AlexanderHD27/oscilloscope-rendering/circuits/dac-pcb/dac-pcb.png

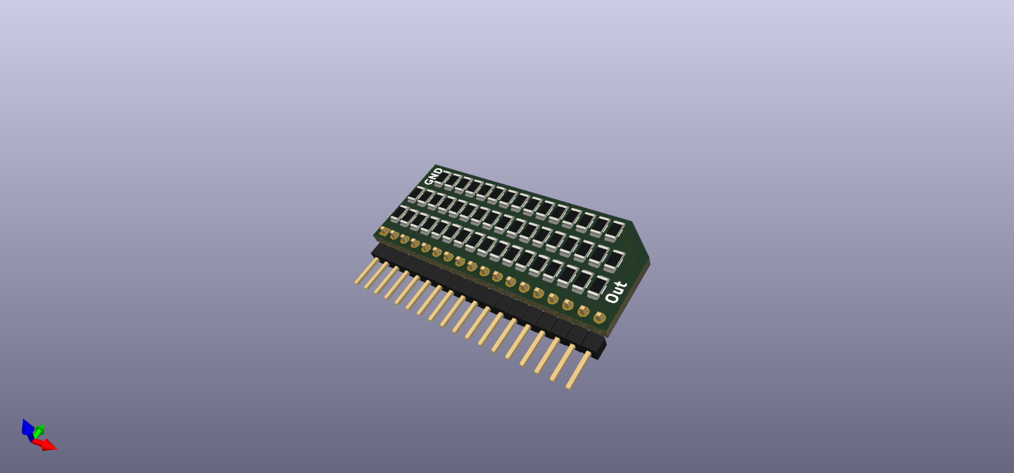
circuits/dac-pcb/dac-pcb.png
