AlexanderHD27/oscilloscope-rendering/tools/Op-Amp_Inverting_Amplifier.svg.png

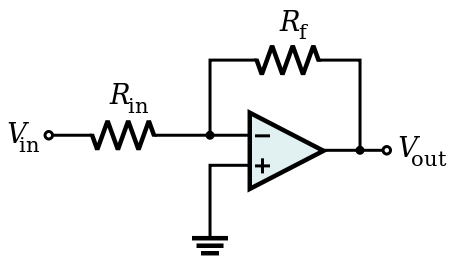
tools/Op-Amp_Inverting_Amplifier.svg.png
