AlexanderHD27/oscilloscope-rendering/circuits/rpi-pico-wiring/rpi-pico-wiring.kicad_pcb

## KiCad design NABU/NABU-01.kicad_sch


Parts:
C1, C2: 680pF
J17: 4K/8K_JUMPER
PH1: NABU-01
R1: 680Ω
R2, R3, R4: 3.3K
R5, R6, R7: 33Ω
U9, U37, U57: LS32
U28: LS38
U38: LP76-57
U39: LS00
U42: HM4864-2_(U42..U49)
U50: 33Ω
U51: LS157_(U51)
U52: LS157_(U52)
U53: 2732/2764
U54: Z80
U55: LS260
U56: LS04
U58: LS74

Connections:
3.58: U58.
+5V: R1.1, R2.1, R3.1, R4.1, U53., U54., U58.
A0: U52., U53., U54.
A1: U52., U53., U54.
A2: U52., U53., U54.
A3: U52., U53., U54.
A4: U51., U53., U54.
A5: U51., U53., U54.
A6: U51., U53., U54.
A7: U51., U53., U54.
A8: U52., U53., U54.
A9: U52., U53., U54.
A10: U52., U53., U54.
A11: U52., U53., U54.
A12: J17., U51., U53., U54.
A13: U51., U54., U55.
A14: U51., U54., U55.
A15: U51., U54., U55.
CLK: U54., U58.
D0: U42., U53., U54.
D1: U42., U53., U54.
D2: U42., U53., U54.
D3: U42., U53., U54.
D4: U42., U53., U54.
D5: U42., U53., U54.
D6: U42., U53., U54.
D7: U42., U53., U54.
Earth: C1.2, C2.2, J17., U37., U52., U53., U54., U55., U57.
unnamed: C1.1, U9., U57.
unnamed: C2.1, U55., U56., U57., U58.
unnamed: J17., U55.
unnamed: R2.2, U54.
unnamed: R3.2, U54.
unnamed: R4.2, U54.
unnamed: R5.1, U42.
unnamed: R5.2, U38.1, U57.
unnamed: R6.1, U42.
unnamed: R6.2, U37.
unnamed: R7.1, U42.
unnamed: R7.2, U39.
unnamed: U28., U58.
unnamed: U37., U38.10, U39.
unnamed: U38.12, U56.
unnamed: U39., U53., U54., U56., U58.
unnamed: U42., U50.
unnamed: U50., U51., U52.
unnamed: U51., U52.
unnamed: U52., U56.
unnamed: U54., U57.
unnamed: U9., U55., U56., U57.
~INTAK: U37.
~INT: U54.
~IORQ: U37., U54.
~M1: U37., U54.
~RD: U39., U54., U55., U57., U58.
~ROMSEL: U55.
~RST: U54.
~WAIT: R1.2, U28., U54.
~WR: U54., U57.

Notes on the sheet:
20NS
RAM ADDRESS MUX
60NS
WAIT STATE
